Thomas032/cycling-buddy/code/lock_icon.h

#if defined(__AVR__)
    #include <avr/pgmspace.h>
#elif defined(__PIC32MX__)
    #define PROGMEM
#elif defined(__arm__)
    #define PROGMEM
#endif

const unsigned char lock [] PROGMEM = {
	// 'image, 95x110px
	0x00, 0x00, 0x00, 0x00, 0x00, 0x00, 0x00, 0x00, 0x00, 0x00, 0x00, 0x00, 0x00, 0x00, 0x00, 0x00, 
	0x00, 0x00, 0x00, 0x00, 0x00, 0x00, 0x00, 0x00, 0x00, 0x00, 0x00, 0x00, 0x00, 0x00, 0x00, 0x00, 
	0x00, 0x00, 0x00, 0x00, 0x00, 0x00, 0x00, 0x00, 0x00, 0x00, 0x00, 0x00, 0x00, 0x00, 0x00, 0x00, 
	0x00, 0x00, 0x00, 0x00, 0x00, 0x00, 0x00, 0x00, 0x00, 0x00, 0x00, 0x00, 0x00, 0x00, 0x00, 0x00, 
	0x01, 0xff, 0xfe, 0x00, 0x00, 0x00, 0x00, 0x00, 0x00, 0x00, 0x00, 0x00, 0x1f, 0xff, 0xff, 0xc0, 
	0x00, 0x00, 0x00, 0x00, 0x00, 0x00, 0x00, 0x00, 0xff, 0xf8, 0xff, 0xf8, 0x00, 0x00, 0x00, 0x00, 
	0x00, 0x00, 0x00, 0x03, 0xf8, 0x00, 0x01, 0xfe, 0x00, 0x00, 0x00, 0x00, 0x00, 0x00, 0x00, 0x07, 
	0xe0, 0x00, 0x00, 0x3f, 0x80, 0x00, 0x00, 0x00, 0x00, 0x00, 0x00, 0x1f, 0x80, 0x00, 0x00, 0x0f, 
	0xc0, 0x00, 0x00, 0x00, 0x00, 0x00, 0x00, 0x7e, 0x00, 0x1f, 0xc0, 0x01, 0xf0, 0x00, 0x00, 0x00, 
	0x00, 0x00, 0x00, 0xf8, 0x01, 0xff, 0xfc, 0x00, 0xf8, 0x00, 0x00, 0x00, 0x00, 0x00, 0x01, 0xf0, 
	0x0f, 0xff, 0xff, 0xc0, 0x3c, 0x00, 0x00, 0x00, 0x00, 0x00, 0x03, 0xc0, 0x3f, 0xe0, 0x3f, 0xe0, 
	0x1e, 0x00, 0x00, 0x00, 0x00, 0x00, 0x07, 0x80, 0xfc, 0x00, 0x01, 0xf8, 0x0f, 0x00, 0x00, 0x00, 
	0x00, 0x00, 0x0f, 0x01, 0xf0, 0x00, 0x00, 0x7e, 0x07, 0x80, 0x00, 0x00, 0x00, 0x00, 0x0e, 0x07, 
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
	0x00, 0x03, 0xf0, 0x00, 0x00, 0xf0, 0x00, 0x00, 0x00, 0x00, 0x00, 0x00, 0x00, 0x00, 0x78, 0x00, 
	0x00, 0xe0, 0x00, 0x00, 0x00, 0x00, 0x00, 0x00, 0x00, 0x00, 0x3c, 0x00, 0x01, 0xc0, 0x00, 0x00, 
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
};
